Yaccoub/Smart_Pump/documentation/pictures/pictures/1617369345657.jpg

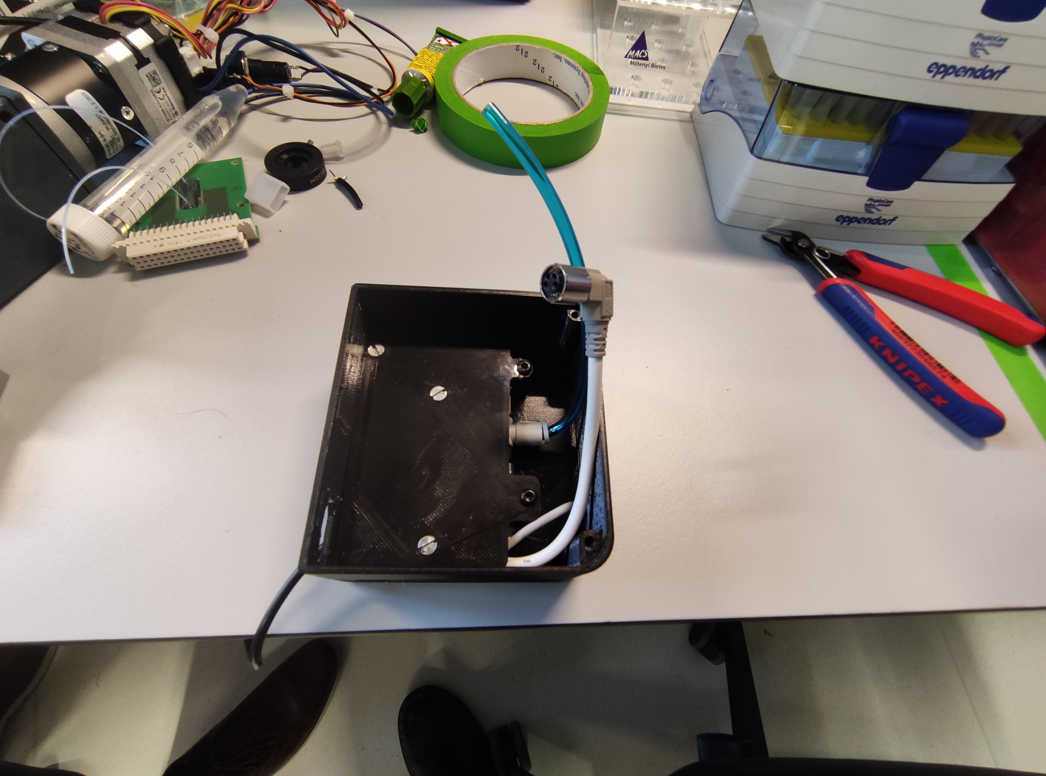
documentation/pictures/pictures/1617369345657.jpg
